sai-ydev/smart_mop/SmartMop.cydsn/common_bmi270.h

/**\
 * Copyright (c) 2021 Bosch Sensortec GmbH. All rights reserved.
 *
 * SPDX-License-Identifier: BSD-3-Clause
 **/

#ifndef _COMMON_BMI270_H
#define _COMMON_BMI270_H

/*! CPP guard */
#ifdef __cplusplus
extern "C" {
#endif

#include <stdio.h>
#include "bmi2.h"


/*!
 *  @brief Function for reading the sensor's registers through I2C bus.
 *
 *  @param[in] reg_addr     : Register address.
 *  @param[out] reg_data    : Pointer to the data buffer to store the read data.
 *  @param[in] length       : No of bytes to read.
 *  @param[in] intf_ptr     : Interface pointer
 *
 *  @return Status of execution
 *  @retval = BMI2_INTF_RET_SUCCESS -> Success
 *  @retval != BMI2_INTF_RET_SUCCESS  -> Failure Info
 *
 */
BMI2_INTF_RETURN_TYPE bmi2_i2c_read(uint8_t reg_addr, uint8_t *reg_data, uint32_t len, void *intf_ptr);

/*!
 *  @brief Function for writing the sensor's registers through I2C bus.
 *
 *  @param[in] reg_addr     : Register address.
 *  @param[in] reg_data     : Pointer to the data buffer whose value is to be written.
 *  @param[in] length       : No of bytes to write.
 *  @param[in] intf_ptr     : Interface pointer
 *
 *  @return Status of execution
 *  @retval = BMI2_INTF_RET_SUCCESS -> Success
 *  @retval != BMI2_INTF_RET_SUCCESS  -> Failure Info
 *
 */
BMI2_INTF_RETURN_TYPE bmi2_i2c_write(uint8_t reg_addr, const uint8_t *reg_data, uint32_t len, void *intf_ptr);



/*!
 * @brief This function provides the delay for required time (Microsecond) as per the input provided in some of the
 * APIs.
 *
 *  @param[in] period       : The required wait time in microsecond.
 *  @param[in] intf_ptr     : Interface pointer
 *
 *  @return void.
 *
 */
void bmi2_delay_us(uint32_t period, void *intf_ptr);

/*!
 *  @brief Function to select the interface between SPI and I2C.
 *
 *  @param[in] bma  : Structure instance of bmi2_dev
 *  @param[in] intf : Interface selection parameter
 *
 *  @return Status of execution
 *  @retval 0 -> Success
 *  @retval < 0 -> Failure Info
 */
int8_t bmi2_interface_init(struct bmi2_dev *bma, uint8_t intf);





#ifdef __cplusplus
}
#endif /* End of CPP guard */

#endif /* _COMMON_BMI270_H */
